andraz213/MushroomLamp/assets/photo2.jpg

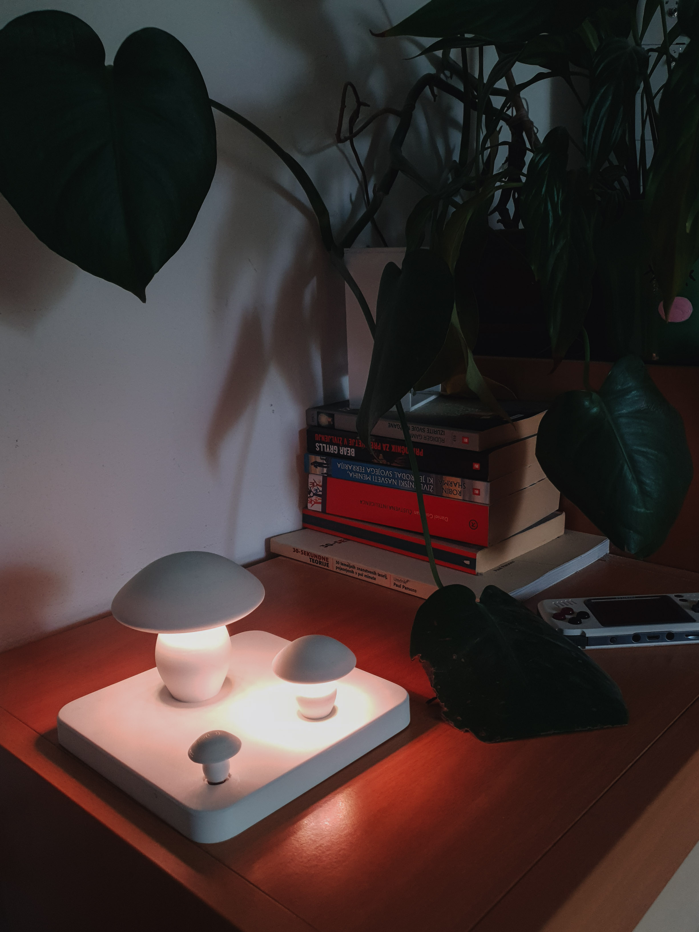
assets/photo2.jpg
