andraz213/MushroomLamp/code/mushroom_lights_esp8266/global_defines.h

#ifndef GLOBAL_DEFINES_H
#define GLOBAL_DEFINES_H

#define ROTARY_PRESS 12
#define ROTARY_A     13
#define ROTARY_B     14
#define MOSFET_PIN   2
#define LED_PIN      0

#define NUM_STATES   4



#endif
